matheussantosmonteiro12/GSM-Weather-Station/Fotos/esta2.jpg

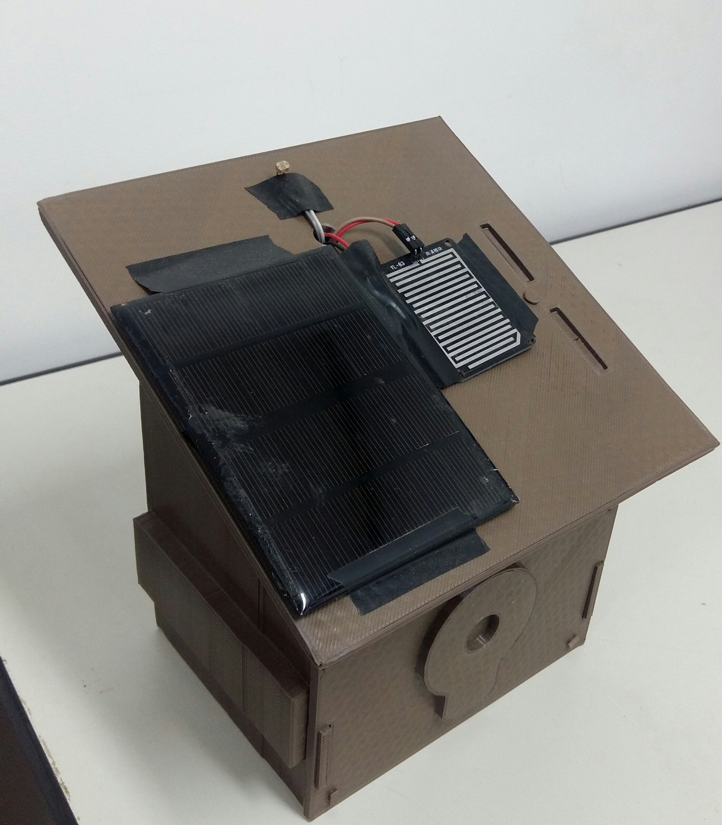
Fotos/esta2.jpg
