matheussantosmonteiro12/GSM-Weather-Station/Fotos/grafhumy.png

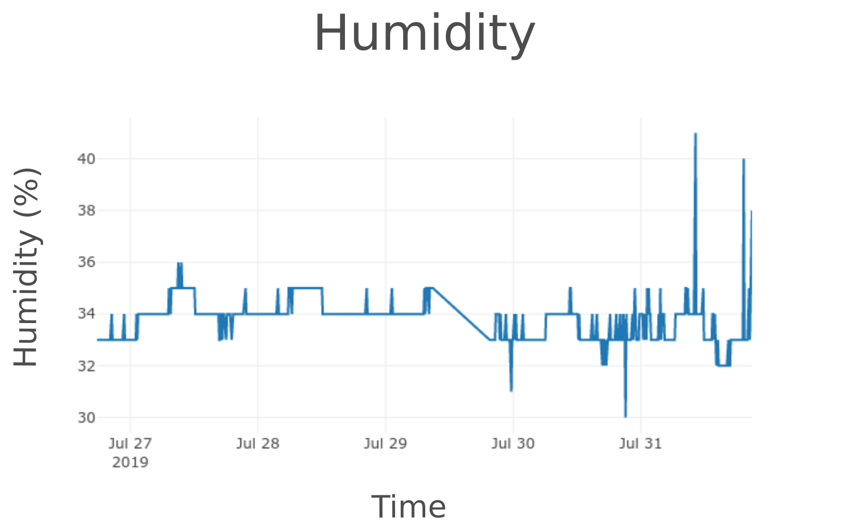
Fotos/grafhumy.png
