matheussantosmonteiro12/GSM-Weather-Station/Fotos/Power.png

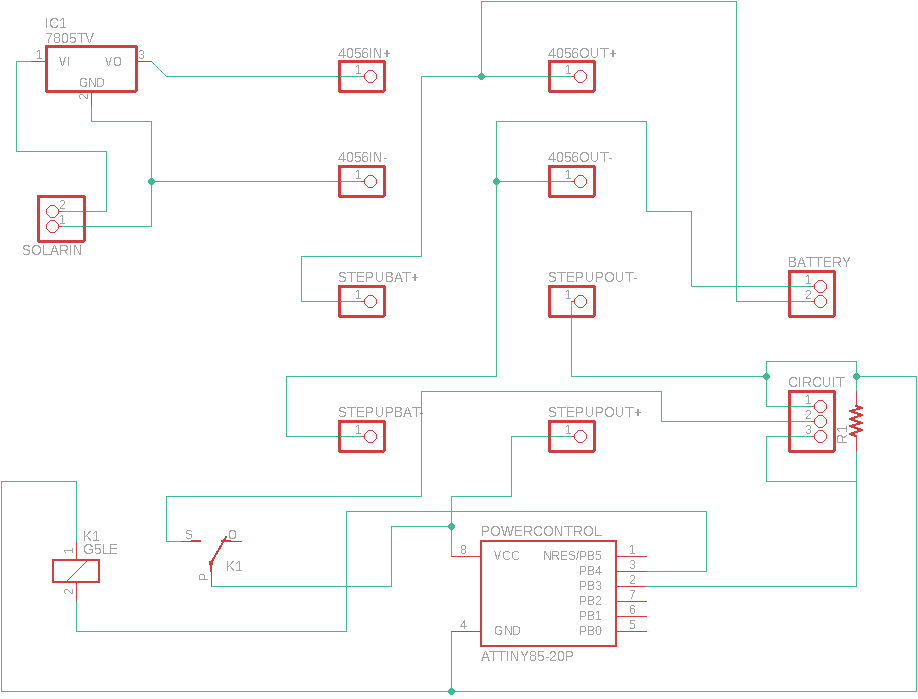
Fotos/Power.png
