matheussantosmonteiro12/GSM-Weather-Station/Fotos/protoDoCircutAment.png

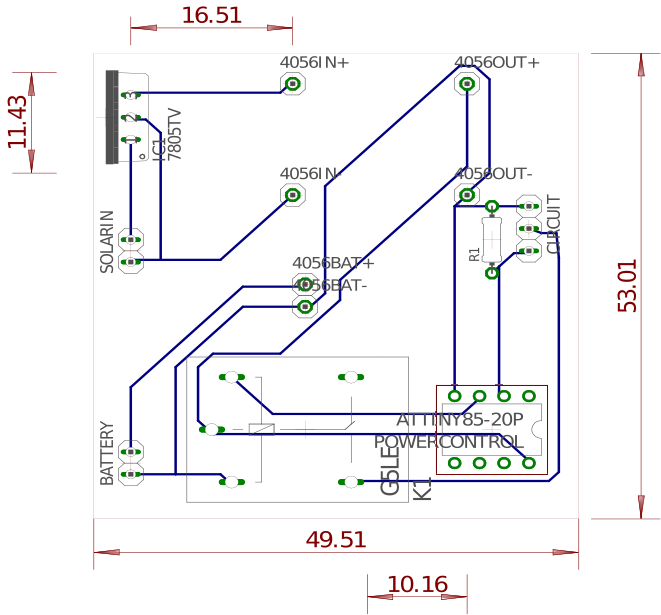
Fotos/protoDoCircutAment.png
