matheussantosmonteiro12/GSM-Weather-Station/Fotos/temperatura.png

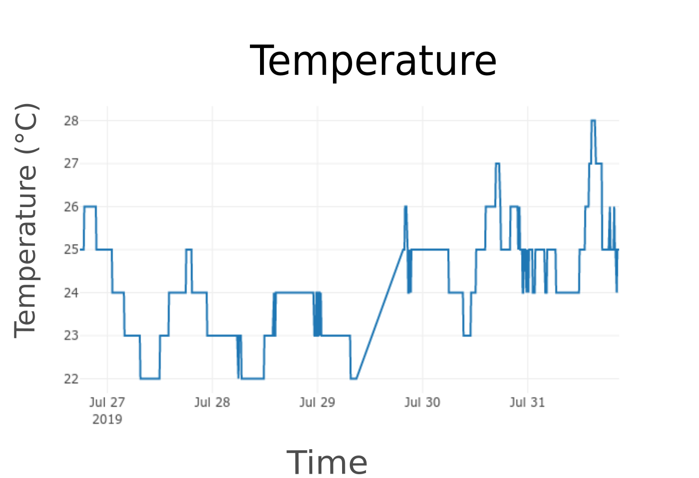
Fotos/temperatura.png
