matheussantosmonteiro12/GSM-Weather-Station/Fotos/wether_box.png

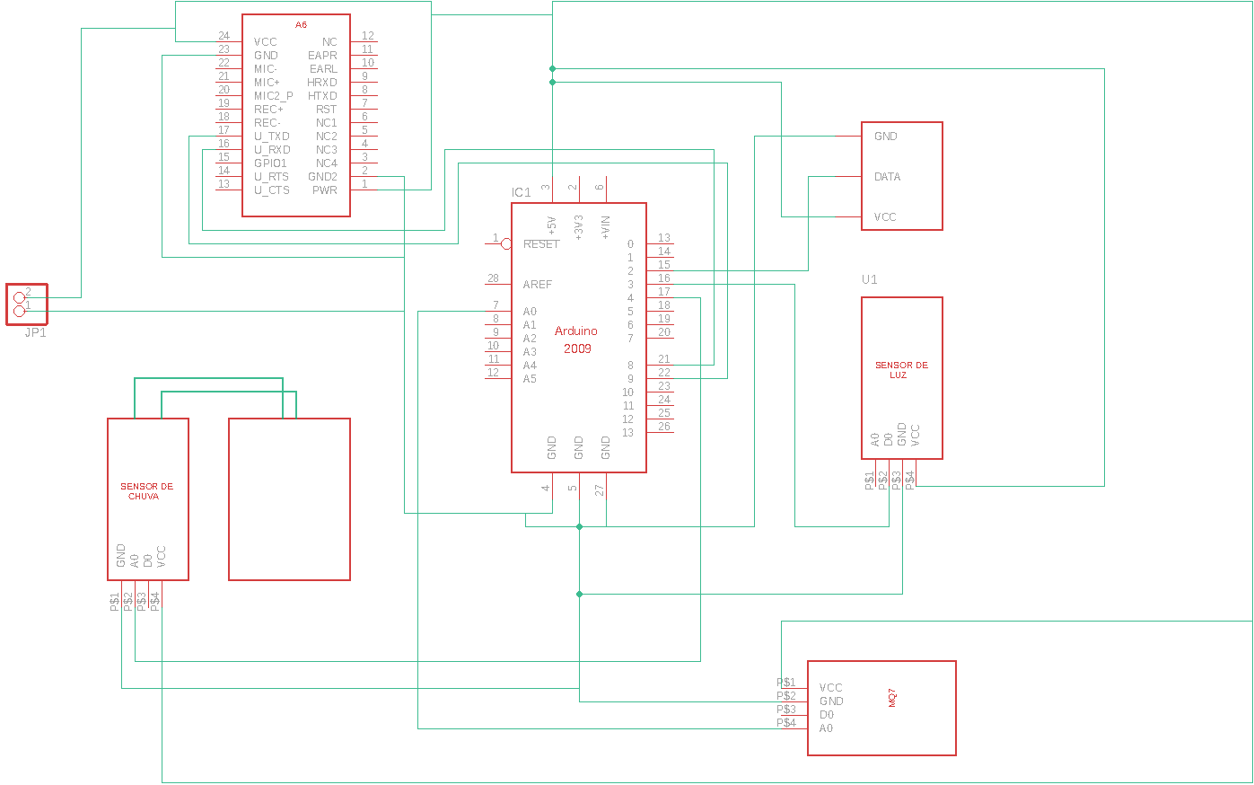
Fotos/wether_box.png
